ibnuda/Gurindam/sandwich/2u.dxf

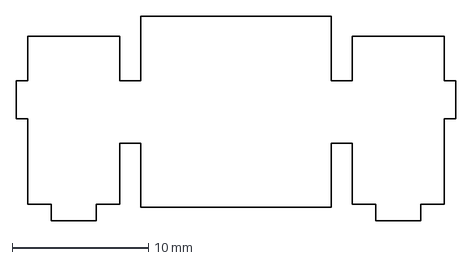
[picture p18: CAD file, 2021-12-01]
sandwich/2u.dxf
32.2 x 15.0 mm
