ibnuda/Gurindam/sandwich/plates-v2/top-plate.dxf

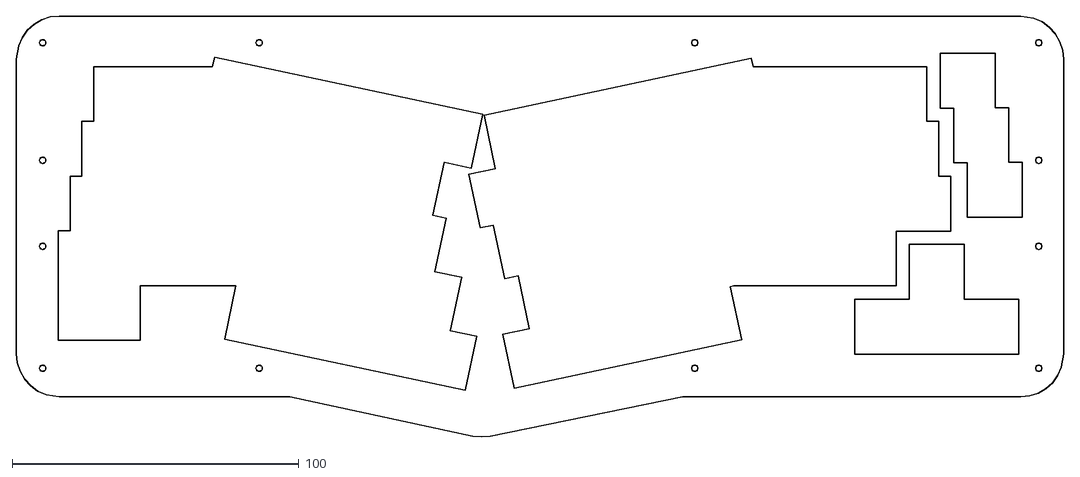
[picture p19: CAD file, 2021-12-23, an earlier design]
sandwich/plates-v2/top-plate.dxf
365.3 x 146.8
