ibnuda/Gurindam/sandwich/plates/plate-middle.dxf

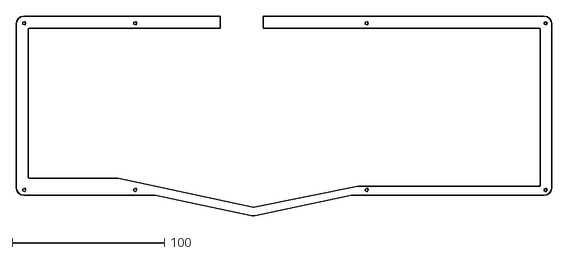
[picture p20: CAD file, 2021-12-01, an earlier design]
sandwich/plates/plate-middle.dxf
352.0 x 131.0
