ibnuda/Gurindam/sandwich/plates-v2/feet-2.dxf

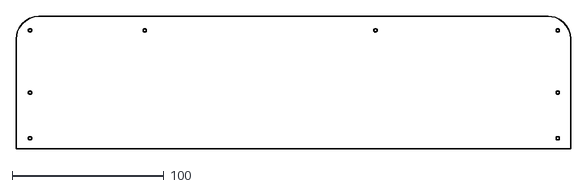
[picture p21: CAD file, 2021-12-23, an earlier design]
sandwich/plates-v2/feet-2.dxf
365.3 x 87.3
